fujiihc/IICPP_Clone/IICPP_Simul/DRG_Classic/EQ_Board/EQ_Board.kicad_sch

## KiCad design IICPP_Simul/DRG_Classic/EQ_Board/EQ_Board.kicad_sch (2025-04-08)

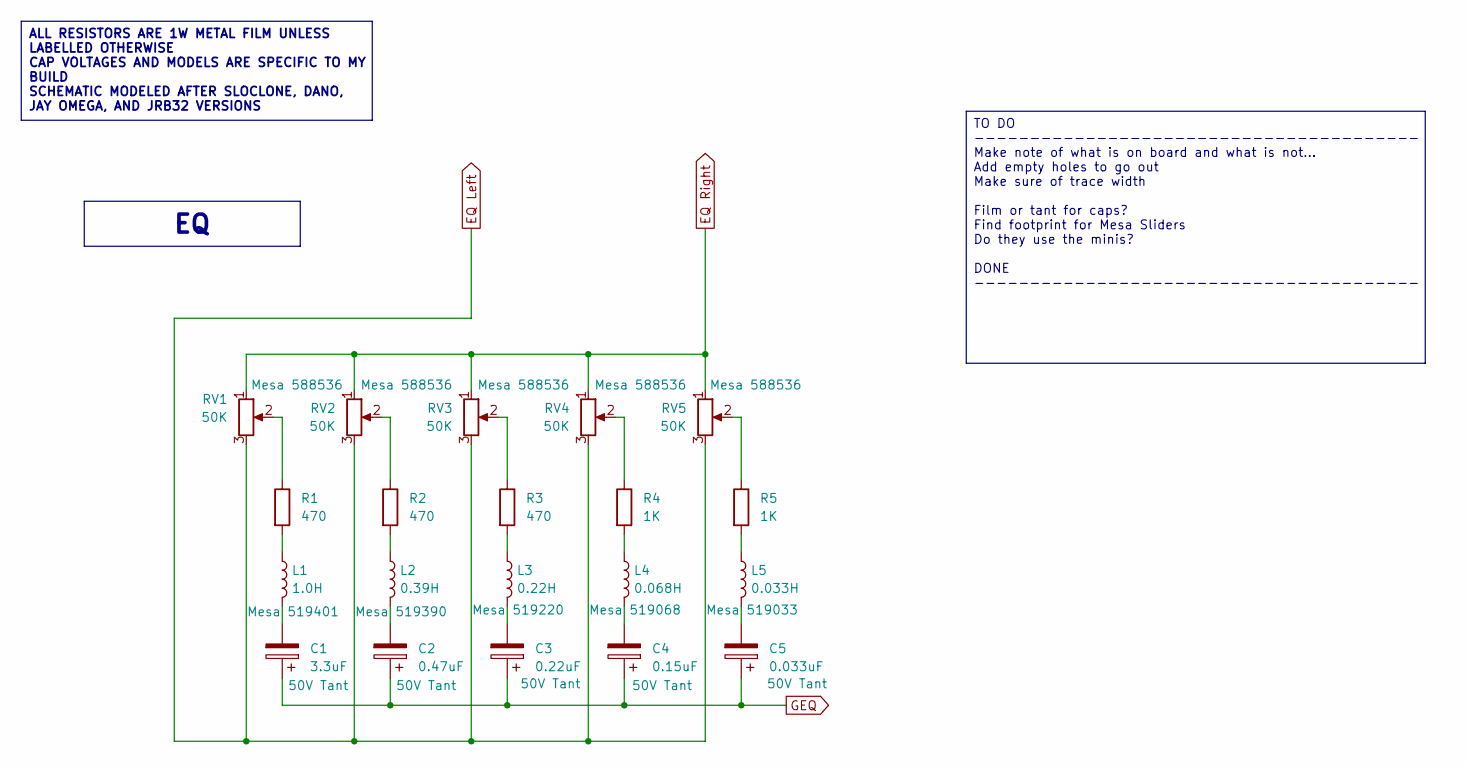
[picture p15: schematic EQ_Board.kicad_sch]

Parts:
C1: 3.3uF
C2: 0.47uF
C3: 0.22uF
C4: 0.15uF
C5: 0.033uF
L1: 1.0H
L2: 0.39H
L3: 0.22H
L4: 0.068H
L5: 0.033H
R1, R2, R3: 470
R4, R5: 1K
RV1, RV2, RV3, RV4, RV5: 50K

Connections:
EQ Left: RV1.3, RV2.3, RV3.3, RV4.3, RV5.3
EQ Right: RV1.1, RV2.1, RV3.1, RV4.1, RV5.1
GEQ: C1.1, C2.1, C3.1, C4.1, C5.1
unnamed: C1.2, L1.2
unnamed: C2.2, L2.2
unnamed: C3.2, L3.2
unnamed: C4.2, L4.2
unnamed: C5.2, L5.2
unnamed: L1.1, R1.2
unnamed: L2.1, R2.2
unnamed: L3.1, R3.2
unnamed: L4.1, R4.2
unnamed: L5.1, R5.2
unnamed: R1.1, RV1.2
unnamed: R2.1, RV2.2
unnamed: R3.1, RV3.2
unnamed: R4.1, RV4.2
unnamed: R5.1, RV5.2

Notes on the sheet:
ALL RESISTORS ARE 1W METAL FILM UNLESS LABELLED OTHERWISE CAP VOLTAGES AND MODELS ARE SPECIFIC TO MY BUILD SCHEMATIC MODELED AFTER SLOCLONE, DANO, JAY OMEGA, AND JRB32 VERSIONS
TO DO ---------------------------------------- Make note of what is on board and what is not... Add empty holes to go out Make sure of trace width Film or tant for caps? Find footprint for Mesa Sliders Do they use the minis? DONE ----------------------------------------
