fujiihc/IICPP_Clone/IICPP_Simul/DRG_Classic/EQ_Driver_Board/EQ_Driver_Board.kicad_sch

## KiCad design IICPP_Simul/DRG_Classic/EQ_Driver_Board/EQ_Driver_Board.kicad_sch (2025-04-08)

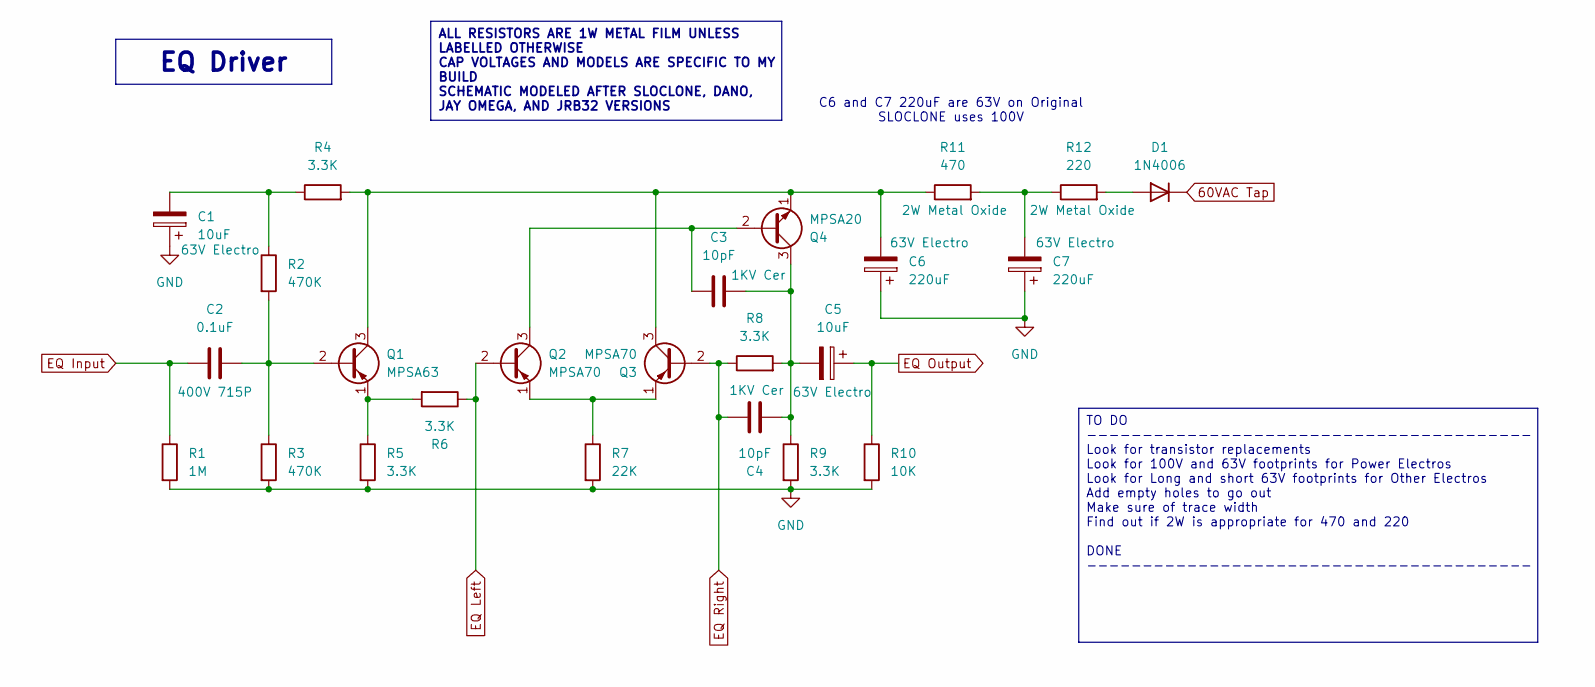
[picture p16: schematic EQ_Driver_Board.kicad_sch]

Parts:
C1, C5: 10uF
C2: 0.1uF
C3, C4: 10pF
C6, C7: 220uF
D1: 1N4006; D_DO-41_SOD81_P10.16mm_Horizontal
Q1: MPSA63; TO-92_Inline
Q2, Q3: MPSA70; TO-92_Inline
Q4: MPSA20; TO-92_Inline
R1: 1M
R2, R3: 470K
R4, R5, R6, R8, R9: 3.3K
R7: 22K
R10: 10K
R11: 470
R12: 220

Connections:
60VAC Tap: D1.1 (K)
EQ Input: C2.1, R1.1
EQ Left: Q2.2 (B), R6.1
EQ Output: C5.1, R10.1
EQ Right: C4.1, Q3.2 (B), R8.1
GND: C1.1, C6.1, C7.1, R1.2, R3.2, R5.2, R7.2, R9.2, R10.2
unnamed: C1.2, R2.1, R4.1
unnamed: C2.2, Q1.2 (B), R2.2, R3.1
unnamed: C3.1, Q2.3 (C), Q4.2 (B)
unnamed: C3.2, C4.2, C5.2, Q4.3 (C), R8.2, R9.1
unnamed: C6.2, Q1.3 (C), Q3.3 (C), Q4.1 (E), R4.2, R11.1
unnamed: C7.2, R11.2, R12.1
unnamed: D1.2 (A), R12.2
unnamed: Q1.1 (E), R5.1, R6.2
unnamed: Q2.1 (E), Q3.1 (E), R7.1

Notes on the sheet:
C6 and C7 220uF are 63V on Original SLOCLONE uses 100V
EQ Driver
ALL RESISTORS ARE 1W METAL FILM UNLESS LABELLED OTHERWISE CAP VOLTAGES AND MODELS ARE SPECIFIC TO MY BUILD SCHEMATIC MODELED AFTER SLOCLONE, DANO, JAY OMEGA, AND JRB32 VERSIONS
TO DO ---------------------------------------- Look for transistor replacements Look for 100V and 63V footprints for Power Electros Look for Long and short 63V footprints for Other Electros Add empty holes to go out Make sure of trace width Find out if 2W is appropriate for 470 and 220 DONE -------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
