fujiihc/IICPP_Clone/IICPP_Simul/DRG_Classic/Preamp_Board/Preamp_Board.kicad_sch

## KiCad design IICPP_Simul/DRG_Classic/Preamp_Board/Preamp_Board.kicad_sch (2025-04-08)

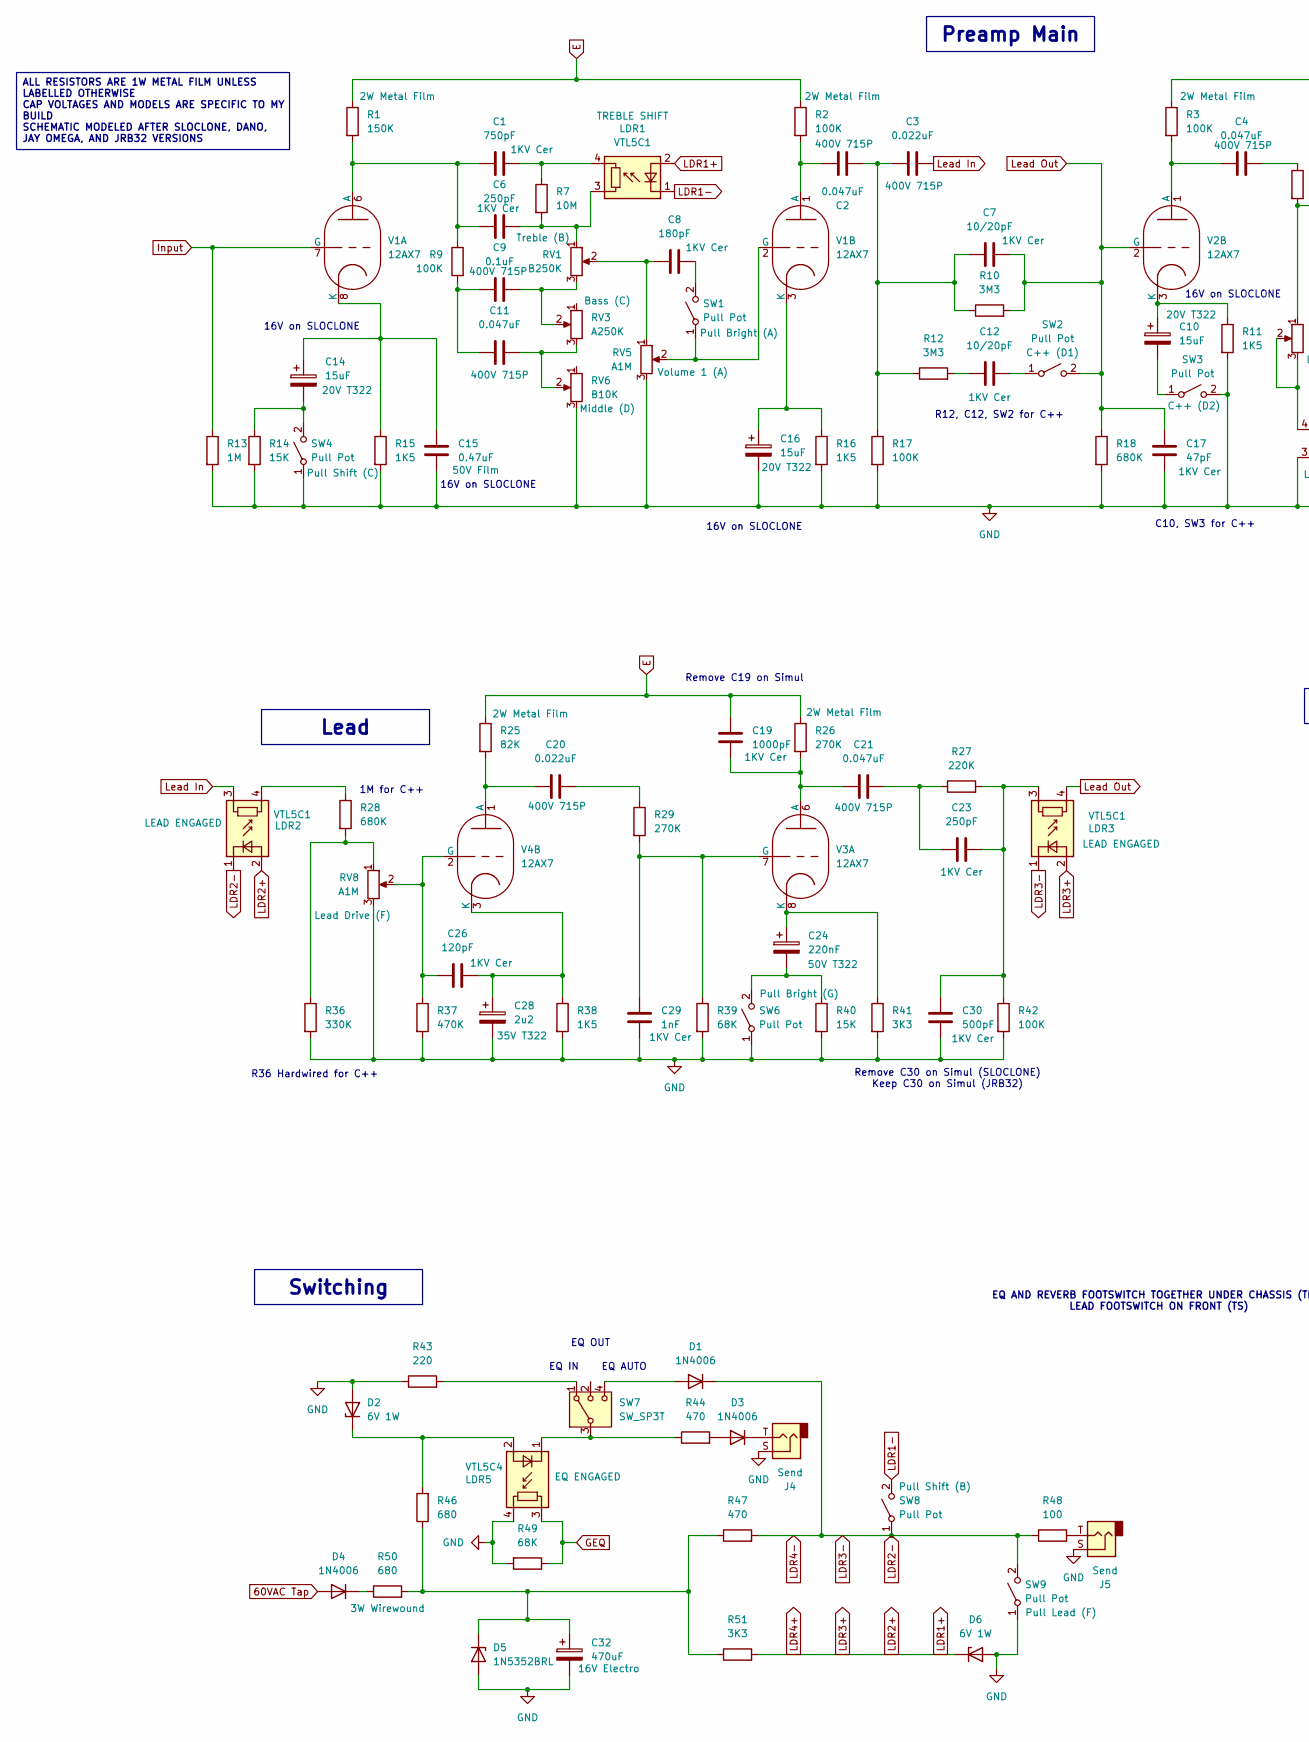
[picture p17: schematic Preamp_Board.kicad_sch, part in row 1, column 1]

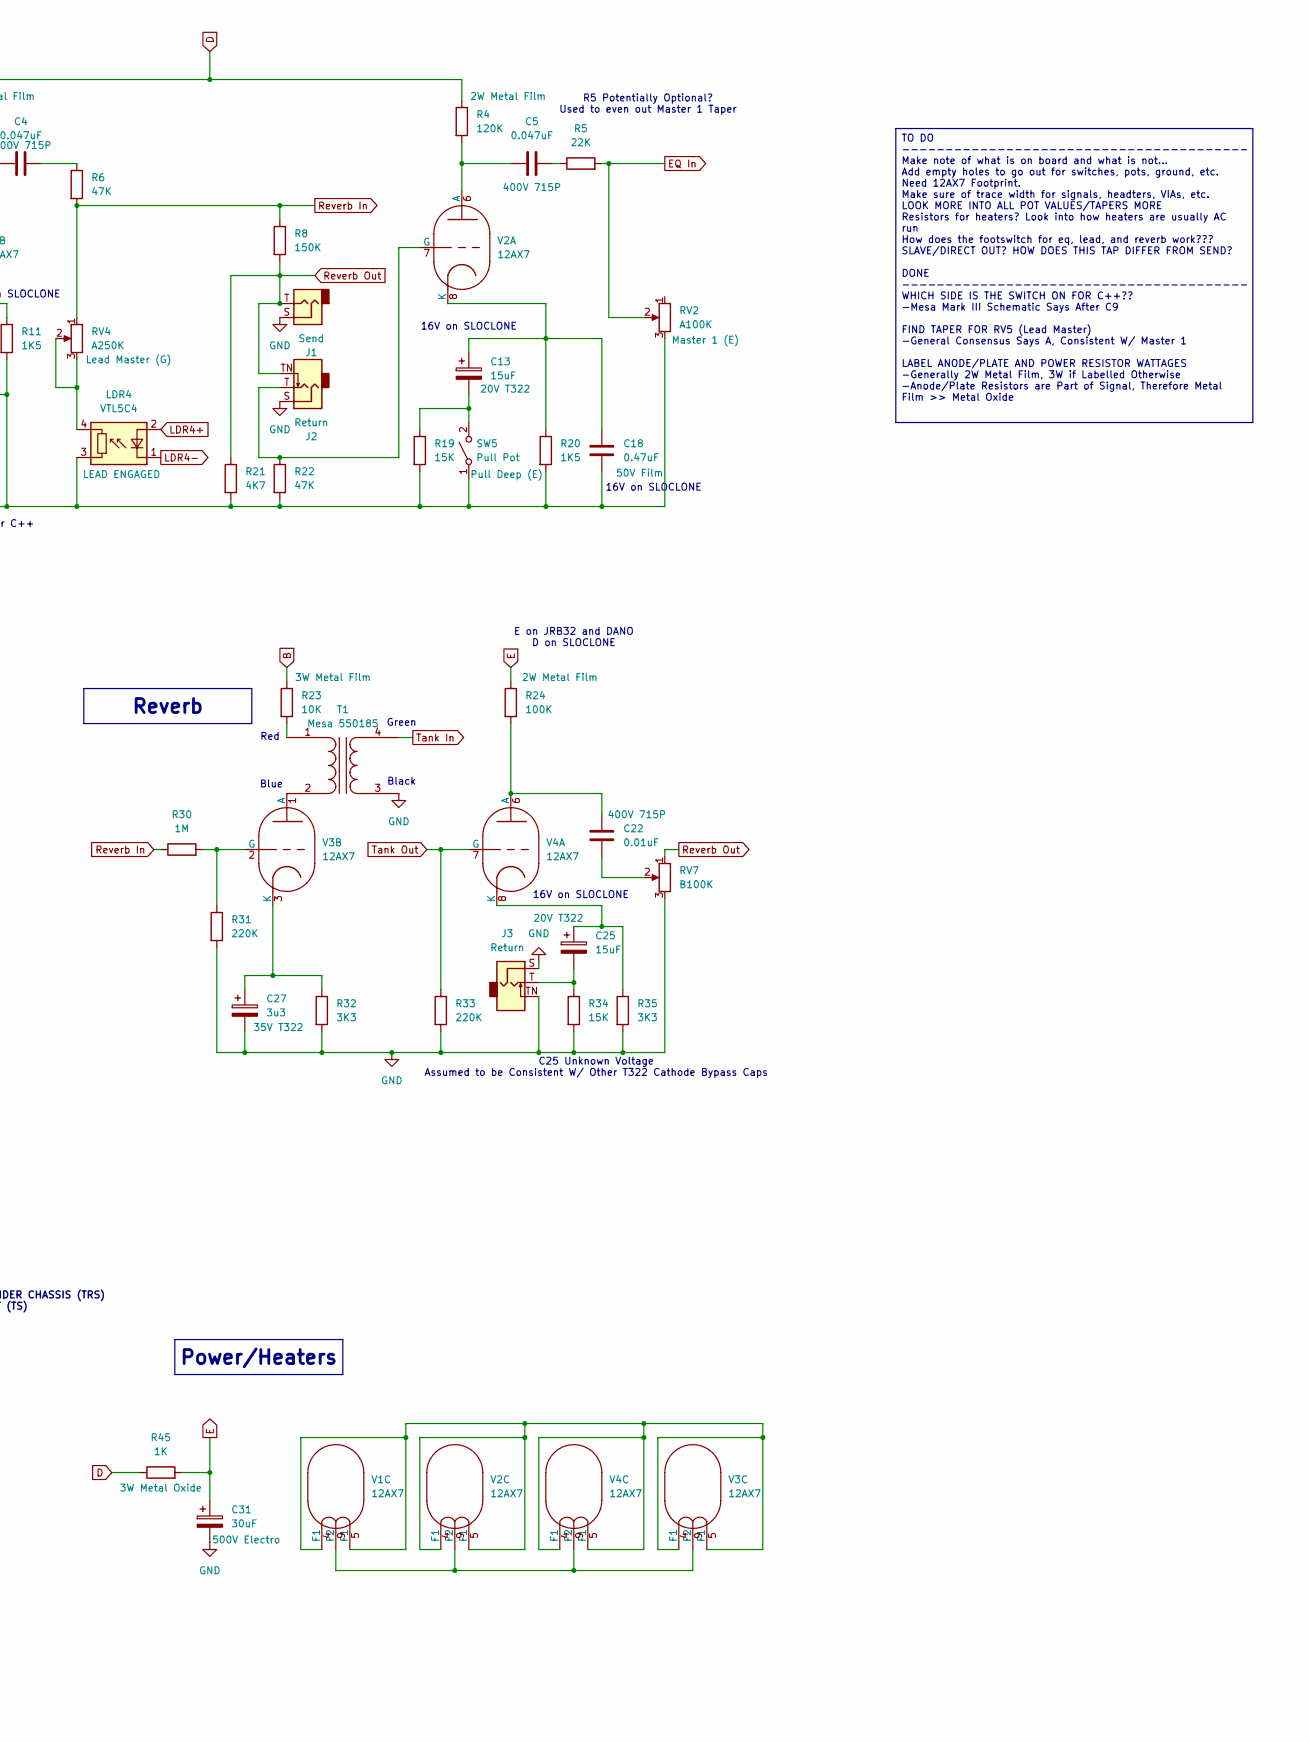
[picture p18: schematic Preamp_Board.kicad_sch, part in row 1, column 2]

Parts:
C1: 750pF
C2, C4, C5, C11, C21: 0.047uF
C3, C20: 0.022uF
C6, C23: 250pF
C7, C12: 10/20pF
C8: 180pF
C9: 0.1uF
C10, C13, C14, C16, C25: 15uF
C15, C18: 0.47uF
C17: 47pF
C19: 1000pF
C22: 0.01uF
C24: 220nF
C26: 120pF
C27: 3u3
C28: 2u2
C29: 1nF
C30: 500pF
C31: 30uF
C32: 470uF
D1, D3, D4: 1N4006; D_DO-41_SOD81_P10.16mm_Horizontal
D2, D6: 6V 1W
D5: 1N5352BRL
J1, J4, J5: Send
J2, J3: Return
LDR1, LDR2, LDR3: VTL5C1; PerkinElmer_VTL5C
LDR4, LDR5: VTL5C4; PerkinElmer_VTL5C
R1, R8: 150K
R2, R3, R9, R17, R24, R42: 100K
R4: 120K
R5: 22K
R6, R22: 47K
R7: 10M
R10, R12: 3M3
R11, R15, R16, R20, R38: 1K5
R13, R30: 1M
R14, R19, R34, R40: 15K
R18, R28: 680K
R21: 4K7
R23: 10K
R25: 82K
R26, R29: 270K
R27, R31, R33: 220K
R32, R35, R41, R51: 3K3
R36: 330K
R37: 470K
R39, R49: 68K
R43: 220
R44, R47: 470
R45: 1K
R46, R50: 680
R48: 100
RV1: B250K
RV2: A100K
RV3, RV4: A250K
RV5, RV8: A1M
RV6: B10K
RV7: B100K
SW1, SW2, SW3, SW4, SW5, SW6, SW8, SW9: Pull Pot
SW7: SW_SP3T
T1: Mesa 550185
V1, V2, V3, V4: 12AX7; Valve_Noval_P

Connections:
60VAC Tap: D4.2 (A)
B: R23.1
D: R3.1, R4.1, R45.1
E: C19.1, C31.1, R1.1, R2.1, R24.1, R25.1, R26.1, R45.2
EQ In: R5.2, RV2.2
GEQ: LDR5.3, R49.1
GND: C15.2, C16.2, C17.2, C18.2, C27.2, C28.2, C29.2, C30.2, C31.2, C32.2, D2.2 (A), D5.2 (A), D6.2 (A), J1.S, J2.S, J3.S, J3.TN, J4.S, J5.S, LDR4.3, LDR5.4, R11.2, R13.2, R14.2, R15.2, R16.2, R17.2, R18.2, R19.2, R20.2, R21.2, R22.2, R31.2, R32.2, R33.2, R34.2, R35.2, R36.2, R37.2, R38.2, R39.2, R40.2, R41.2, R42.2, R43.1, R49.2, RV2.3, RV5.3, RV6.3, RV7.3, RV8.3, SW3.2 (B), SW4.1 (A), SW5.1 (A), SW6.1 (A), SW9.1 (A), T1.3 (SA)
Input: R13.1, V1.7 (G)
LDR1+: D6.1 (K), LDR1.2 (+), LDR2.2 (+), LDR3.2 (+), LDR4.2 (+), R51.2
LDR1-: LDR1.1 (-), SW8.2 (B)
LDR2-: D1.1 (K), LDR2.1 (-), LDR3.1 (-), LDR4.1 (-), R47.2, R48.1, SW8.1 (A), SW9.2 (B)
Lead In: C3.2, LDR2.3
Lead Out: C7.2, C17.1, LDR3.4, R10.2, R18.1, SW2.2 (B), V2.2 (G)
unnamed: C1.1, C6.1, R1.2, R9.1, V1.6 (A)
unnamed: C1.2, LDR1.4, R7.1
unnamed: C2.1, R2.2, V1.1 (A)
unnamed: C2.2, C3.1, C7.1, R10.1, R12.1, R17.1
unnamed: C4.1, R3.2, V2.1 (A)
unnamed: C4.2, R6.1
unnamed: C5.1, R4.2, V2.6 (A)
unnamed: C5.2, R5.1
unnamed: C6.2, LDR1.3, R7.2, RV1.1
unnamed: C8.1, RV1.2, RV5.1
unnamed: C8.2, SW1.2 (B)
unnamed: C9.2, RV1.3, RV3.2
unnamed: C10.1, R11.1, V2.3 (K)
unnamed: C10.2, SW3.1 (A)
unnamed: C9.1, C11.1, R9.2
unnamed: C11.2, RV3.3, RV6.2
unnamed: C12.1, R12.2
unnamed: C12.2, SW2.1 (A)
unnamed: C13.1, C18.1, R20.1, V2.8 (K)
unnamed: C13.2, R19.1, SW5.2 (B)
unnamed: C14.1, C15.1, R15.1, V1.8 (K)
unnamed: C14.2, R14.1, SW4.2 (B)
unnamed: C16.1, R16.1, V1.3 (K)
unnamed: C19.2, C21.1, R26.2, V3.6 (A)
unnamed: C20.1, R25.2, V4.1 (A)
unnamed: C20.2, R29.1
unnamed: C21.2, C23.1, R27.1
unnamed: C22.1, R24.2, V4.6 (A)
unnamed: C22.2, RV7.2
unnamed: C23.2, C30.1, LDR3.3, R27.2, R42.1
unnamed: C24.1, R41.1, V3.8 (K)
unnamed: C24.2, R40.1, SW6.2 (B)
unnamed: C25.1, R35.1, V4.8 (K)
unnamed: C25.2, J3.T, R34.1
unnamed: C26.1, R37.1, RV8.2, V4.2 (G)
unnamed: C26.2, C28.1, R38.1, V4.3 (K)
unnamed: C27.1, R32.1, V3.3 (K)
unnamed: C29.1, R29.2, R39.1, V3.7 (G)
unnamed: C32.1, D5.1 (K), R46.1, R47.1, R50.2, R51.1
unnamed: D1.2 (A), SW7.4
unnamed: D2.1 (K), LDR5.2 (+), R46.2
unnamed: D3.1 (K), J4.T
unnamed: D3.2 (A), R44.2
unnamed: D4.1 (K), R50.1
unnamed: J2.T, R22.1, V2.7 (G)
unnamed: J5.T, R48.2
unnamed: LDR2.4, R28.1
unnamed: LDR4.4, RV4.2, RV4.3
unnamed: LDR5.1 (-), R44.1, SW7.3
unnamed: R23.2, T1.1 (AA)
unnamed: R28.2, R36.1, RV8.1
unnamed: R30.2, R31.1, V3.2 (G)
unnamed: R43.2, SW7.1
unnamed: RV5.2, SW1.1 (A), V1.2 (G)
unnamed: T1.2 (AB), V3.1 (A)
unnamed: V1.4 (F1), V1.5 (F1), V2.4 (F1), V2.5 (F1), V3.4 (F1), V3.5 (F1), V4.4 (F1), V4.5 (F1)
unnamed: V1.9 (F2), V2.9 (F2), V3.9 (F2), V4.9 (F2)
Reverb In: R6.2, R8.1, R30.1, RV4.1
Reverb Out: J1.T, J2.TN, R8.2, R21.1, RV7.1
Tank In: T1.4 (SB)
Tank Out: R33.1, V4.7 (G)

Notes on the sheet:
16V on SLOCLONE
EQ AND REVERB FOOTSWITCH TOGETHER UNDER CHASSIS (TRS) LEAD FOOTSWITCH ON FRONT (TS)
EQ AUTO
C25 Unknown Voltage Assumed to be Consistent W/ Other T322 Cathode Bypass Caps
C10, SW3 for C++
Green
R36 Hardwired for C++
Remove C30 on Simul (SLOCLONE) Keep C30 on Simul (JRB32)
EQ OUT
Red
E on JRB32 and DANO D on SLOCLONE
R5 Potentially Optional? Used to even out Master 1 Taper
Remove C19 on Simul
R12, C12, SW2 for C++
EQ IN
Blue
1M for C++
Black
Lead
ALL RESISTORS ARE 1W METAL FILM UNLESS LABELLED OTHERWISE CAP VOLTAGES AND MODELS ARE SPECIFIC TO MY BUILD SCHEMATIC MODELED AFTER SLOCLONE, DANO, JAY OMEGA, AND JRB32 VERSIONS
Switching
Reverb
TO DO ---------------------------------------- Make note of what is on board and what is not... Add empty holes to go out for switches, pots, ground, etc. Need 12AX7 Footprint. Make sure of trace width for signals, headters, VIAs, etc. LOOK MORE INTO ALL POT VALUES/TAPERS MORE Resistors for heaters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
Preamp Main
Power/Heaters
